purewack/numcalcium/docs/res/1.2.png

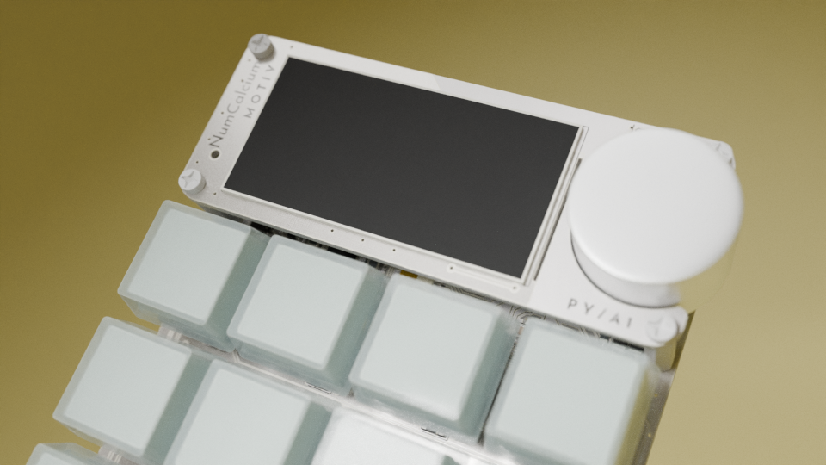
docs/res/1.2.png
