purewack/numcalcium/devlog/pya0-back.png

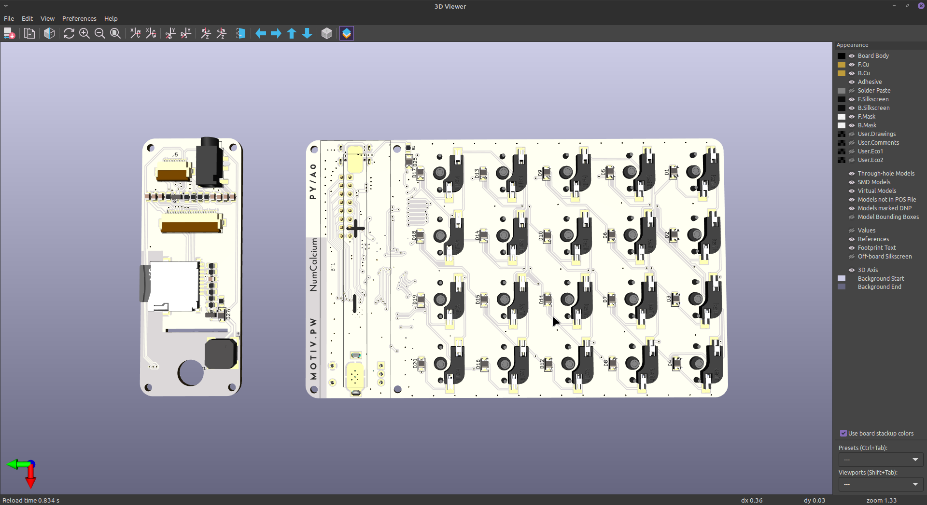
devlog/pya0-back.png
