purewack/numcalcium/devlog/pya0-front-back.png

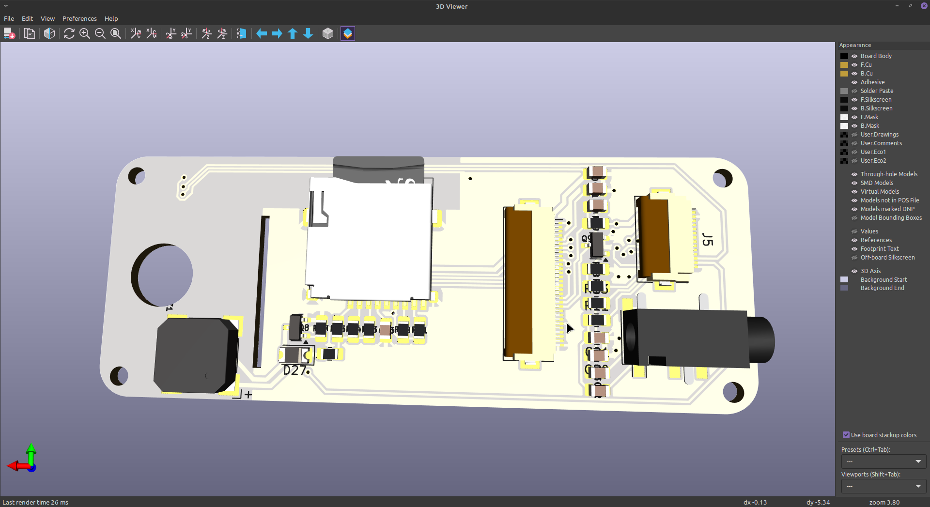
devlog/pya0-front-back.png
