purewack/numcalcium/devlog/pya0-front.png

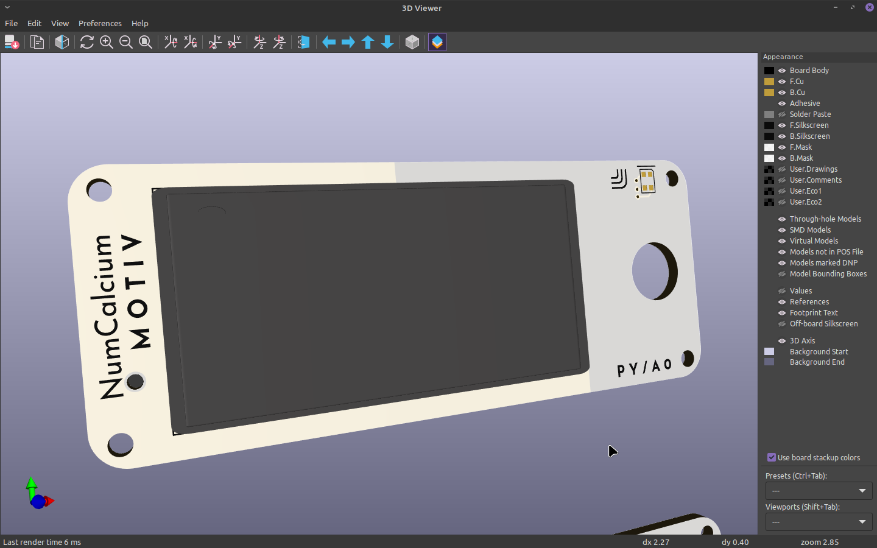
devlog/pya0-front.png
