purewack/numcalcium/devlog/pya0-main-all.png

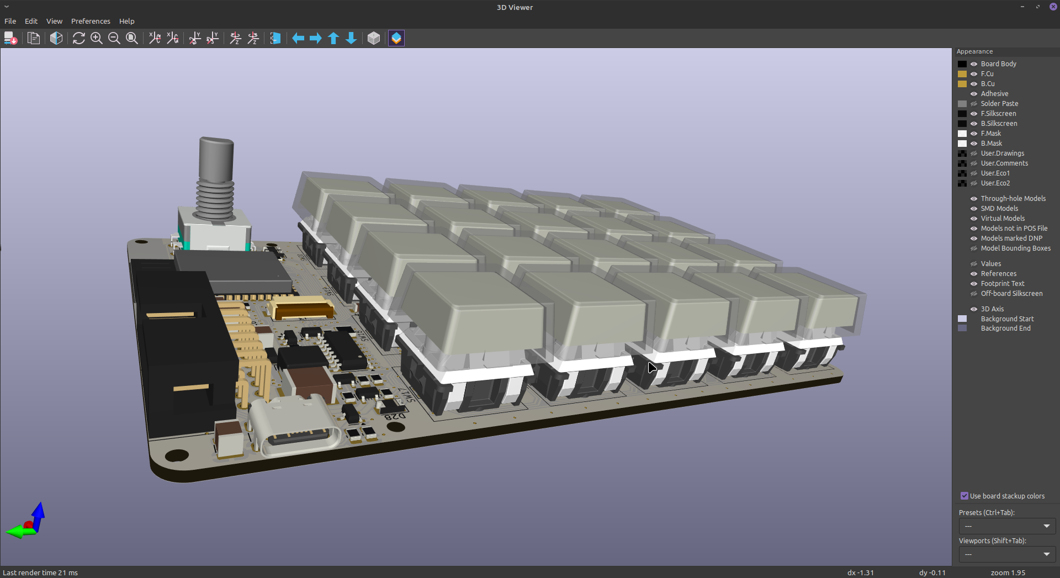
devlog/pya0-main-all.png
