purewack/numcalcium/devlog/pya1-back.png

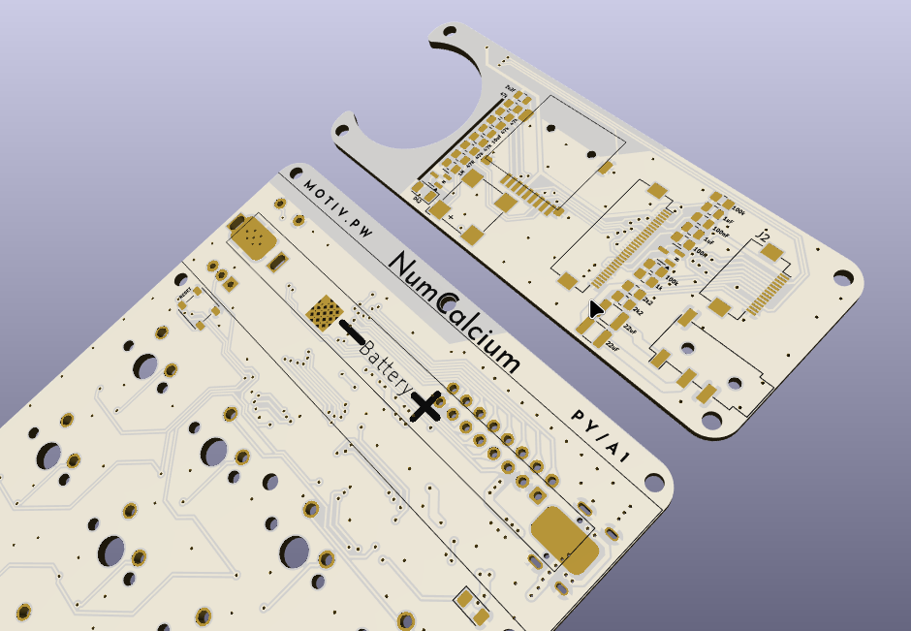
devlog/pya1-back.png
