purewack/numcalcium/devlog/pya1-bcu.png

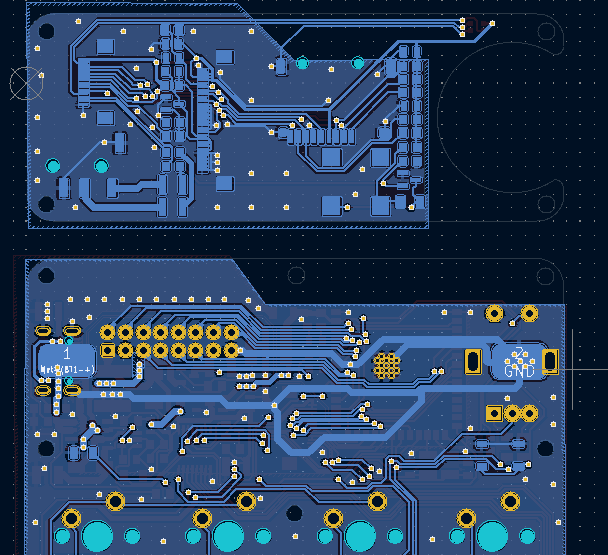
devlog/pya1-bcu.png
