purewack/numcalcium/devlog/pya1-cu.png

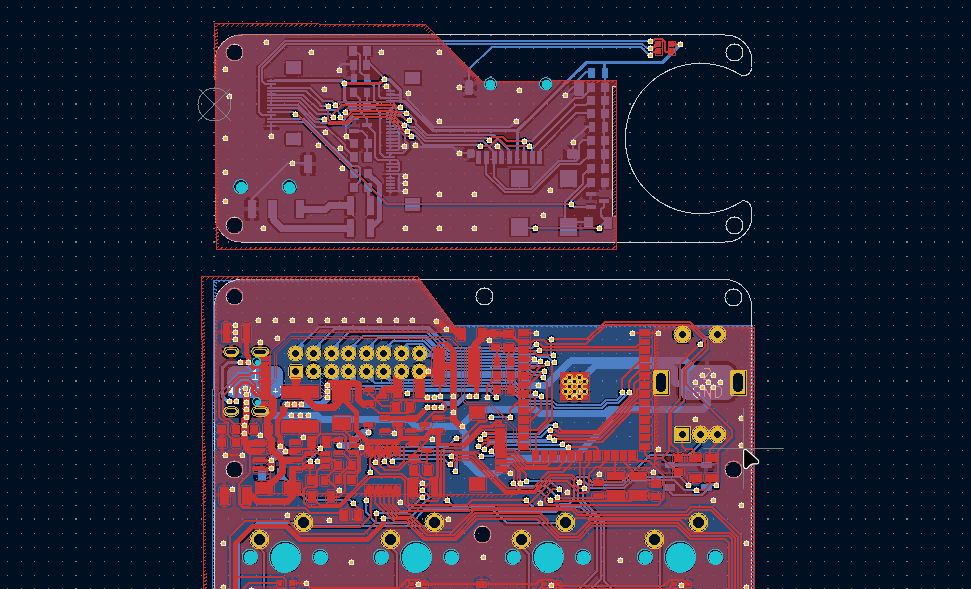
devlog/pya1-cu.png
