purewack/numcalcium/devlog/s3-front.png

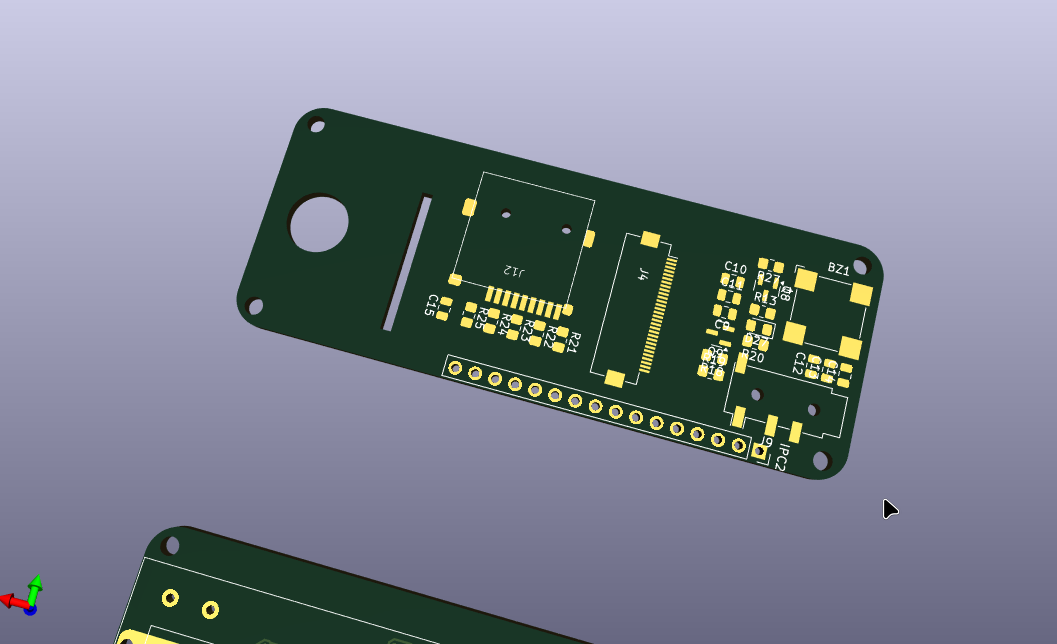
devlog/s3-front.png
