purewack/numcalcium/devlog/s3-gnd-alt-bcu.png

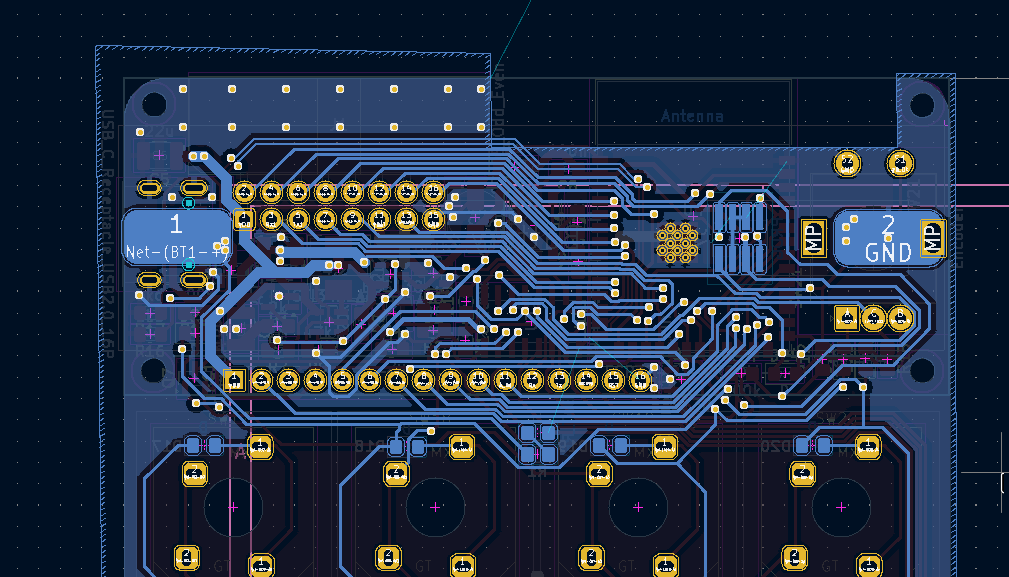
devlog/s3-gnd-alt-bcu.png
