purewack/numcalcium/numcalc/include/defs.h

#pragma once

#define SYS_PDOWN PB5

#define LCD_LIGHT PA6
#define LCD_CS PA4
#define LCD_DC PA3
#define LCD_CK PA5
#define LCD_RST PA2
#define LCD_MOSI PA7

#define SEG_A PB11
#define SEG_B PB10
#define SEG_C PB1
#define SEG_D PB0

#define ROW_A PA14
#define ROW_B PA15
#define ROW_C PB3
#define ROW_D PB4
#define ROW_E PB8
#define ROW_F PB9

#define B_OK PA8

#define GP_A PA0
#define GP_B PA1
#define COMMS_SDA PB7
#define COMMS_SDL PB6
#define COMMS_MOSI PB15
#define COMMS_MISO PB14
#define COMMS_CK   PB13
#define COMMS_CS PB12
#define COMMS_RX PA10
#define COMMS_TX PA9
