purewack/numcalcium/software-pya1/cmodules/board_sdcard.c

/*
 * This file is part of the MicroPython project, http://micropython.org/
 *
 * The MIT License (MIT)
 *
 * Copyright (c) 2019 Nicko van Someren
 *
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
 * THE SOFTWARE IS PROVIDED "AS IS", WITHOUT WARRANTY OF ANY KIND, EXPRESS OR
 * IMPLIED, INCLUDING BUT NOT LIMITED TO THE WARRANTIES OF MERCHANTABILITY,
 * FITNESS FOR A PARTICULAR PURPOSE AND NONINFRINGEMENT. IN NO EVENT SHALL THE
 * AUTHORS OR COPYRIGHT HOLDERS BE LIABLE FOR ANY CLAIM, DAMAGES OR OTHER
 * LIABILITY, WHETHER IN AN ACTION OF CONTRACT, TORT OR OTHERWISE, ARISING FROM,
 * OUT OF OR IN CONNECTION WITH THE SOFTWARE OR THE USE OR OTHER DEALINGS IN
 * THE SOFTWARE.
 */

#include <string.h>

#include "py/runtime.h"
#include "py/mphal.h"
#include "py/mperrno.h"
#include "extmod/vfs_fat.h"

#include "driver/sdspi_host.h"
#include "driver/sdmmc_host.h"
#include "sdmmc_cmd.h"
#include "esp_log.h"

#include "board.h"

// #define DEBUG 0
// #if DEBUG
// #define DEBUG_printf(...) ESP_LOGI("modsdcard", __VA_ARGS__)
// #else
// #define DEBUG_printf(...) (void)0
// #endif

//
// There are three layers of abstraction: host, slot and card.
// Creating an SD Card object will initialise the host and slot.
// Cards gets initialised by ioctl op==1 and de-inited by ioctl 2
// Hosts are de-inited in __del__. Slots do not need de-initing.
//

typedef struct _sdcard_obj_t {
    mp_obj_base_t base;
    mp_int_t flags;
    sdmmc_host_t host;
    // The card structure duplicates the host. It's not clear if we
    // can avoid this given the way that it is copied.
    sdmmc_card_t card;
} sdcard_card_obj_t;

const mp_obj_type_t board_sdcard_type;
// singleton object
static sdcard_card_obj_t sd_instance = {{&board_sdcard_type},0};

#define SDCARD_CARD_FLAGS_HOST_INIT_DONE 0x01
#define SDCARD_CARD_FLAGS_CARD_INIT_DONE 0x02

#define _SECTOR_SIZE(self) (self->card.csd.sector_size)


static esp_err_t sdcard_ensure_card_init(sdcard_card_obj_t *self, bool force) {
    if (force || !(self->flags & SDCARD_CARD_FLAGS_CARD_INIT_DONE)) {
        //DEBUG_printf("  Calling card init\n");

        esp_err_t err = sdmmc_card_init(&(self->host), &(self->card));
        if (err == ESP_OK) {
            self->flags |= SDCARD_CARD_FLAGS_CARD_INIT_DONE;
        } else {
            self->flags &= ~SDCARD_CARD_FLAGS_CARD_INIT_DONE;
        }
        //DEBUG_printf("  Card init returned: %d\n", self->flags);
        
        return err;
    } else {
        return ESP_OK;
    }
}

/******************************************************************************/
// MicroPython bindings
//
// Expose the SD card or MMC as an object with the block protocol.

// Create a new SDCard object
// The driver supports either the host SD/MMC controller (default) or SPI mode
// In both cases there are two "slots". Slot 0 on the SD/MMC controller is
// typically tied up with the flash interface in most ESP32 modules but in
// theory supports 1, 4 or 8-bit transfers. Slot 1 supports only 1 and 4-bit
// transfers. Only 1-bit is supported on the SPI interfaces.
// card = SDCard(slot=1, width=None, present_pin=None, wp_pin=None)

static mp_obj_t board_sdcard_make_new(const mp_obj_type_t *type, size_t n_args, size_t n_kw, const mp_obj_t *args) {
    // check arguments
    enum {
        ARG_freq,
    };
    static const mp_arg_t allowed_args[] = {
        // freq is valid for both SPI and SDMMC interfaces
        { MP_QSTR_freq,     MP_ARG_KW_ONLY | MP_ARG_INT, {.u_int = 40000000} },
    };
    mp_arg_val_t arg_vals[MP_ARRAY_SIZE(allowed_args)];
    mp_map_t kw_args;

    //DEBUG_printf("Making new SDCard\n");
    //DEBUG_printf("  Unpacking arguments\n");

    mp_map_init_fixed_table(&kw_args, n_kw, args + n_args);

    mp_arg_parse_all(n_args, args, &kw_args,
        MP_ARRAY_SIZE(allowed_args), allowed_args, arg_vals);

    if((sd_instance.flags & SDCARD_CARD_FLAGS_HOST_INIT_DONE)) return (mp_obj_t)&sd_instance;

    //DEBUG_printf("  Setting up host configuration\n");

    sd_instance.flags = 0;
    // Note that these defaults are macros that expand to structure
    // constants so we can't directly assign them to fields.
    int freq = arg_vals[ARG_freq].u_int;
    sdmmc_host_t _temp_host = SDSPI_HOST_DEFAULT();
    _temp_host.max_freq_khz = freq / 1000;
    _temp_host.slot = BOARD_SPI_SLOT_INTERNAL;
    sd_instance.host = _temp_host;

    //DEBUG_printf("  Calling host.init()\n");

    check_esp_err(sd_instance.host.init());
    sd_instance.flags |= SDCARD_CARD_FLAGS_HOST_INIT_DONE;

    //DEBUG_printf("  Returning new card object: %p\n", &sd_instance);
    return (mp_obj_t)&sd_instance;
}

static mp_obj_t sd_deinit(mp_obj_t self_in) {
    sdcard_card_obj_t *self = self_in;

    //DEBUG_printf("De-init host\n");

    if (self->flags & SDCARD_CARD_FLAGS_HOST_INIT_DONE) {
        if (self->host.flags & SDMMC_HOST_FLAG_DEINIT_ARG) {
            self->host.deinit_p(self->host.slot);
        } else {
            self->host.deinit();
        }
        // if (self->host.flags & SDMMC_HOST_FLAG_SPI) {
        //     // SD card used a (dedicated) SPI bus, so free that SPI bus.
        //     spi_bus_free(self->host.slot);
        // }
        self->flags &= ~SDCARD_CARD_FLAGS_HOST_INIT_DONE;
    }
    
    return mp_const_none;
}
static MP_DEFINE_CONST_FUN_OBJ_1(sd_deinit_obj, sd_deinit);

static mp_obj_t sd_info(mp_obj_t self_in) {
    sdcard_card_obj_t *self = self_in;
    // We could potential return a great deal more SD card data but it
    // is not clear that it is worth the extra code space to do
    // so. For the most part people only care about the card size and
    // block size.

    check_esp_err(sdcard_ensure_card_init((sdcard_card_obj_t *)self, false));

    uint32_t log_block_nbr = self->card.csd.capacity;
    uint32_t log_block_size = _SECTOR_SIZE(self);

    mp_obj_t tuple[2] = {
        mp_obj_new_int_from_ull((uint64_t)log_block_nbr * (uint64_t)log_block_size),
        mp_obj_new_int_from_uint(log_block_size),
    };
    return mp_obj_new_tuple(2, tuple);
}
static MP_DEFINE_CONST_FUN_OBJ_1(sd_info_obj, sd_info);

static mp_obj_t board_sdcard_readblocks(mp_obj_t self_in, mp_obj_t block_num, mp_obj_t buf) {
    sdcard_card_obj_t *self = self_in;
    mp_buffer_info_t bufinfo;
    esp_err_t err;

    err = sdcard_ensure_card_init((sdcard_card_obj_t *)self, false);
    if (err != ESP_OK) {
        return false;
    }

    mp_get_buffer_raise(buf, &bufinfo, MP_BUFFER_WRITE);
    err = sdmmc_read_sectors(&(self->card), bufinfo.buf, mp_obj_get_int(block_num), bufinfo.len / _SECTOR_SIZE(self));

    return mp_obj_new_bool(err == ESP_OK);
}
static MP_DEFINE_CONST_FUN_OBJ_3(board_sdcard_readblocks_obj, board_sdcard_readblocks);

static mp_obj_t board_sdcard_writeblocks(mp_obj_t self_in, mp_obj_t block_num, mp_obj_t buf) {
    sdcard_card_obj_t *self = self_in;
    mp_buffer_info_t bufinfo;
    esp_err_t err;

    err = sdcard_ensure_card_init((sdcard_card_obj_t *)self, false);
    if (err != ESP_OK) {
        return false;
    }

    mp_get_buffer_raise(buf, &bufinfo, MP_BUFFER_READ);
    err = sdmmc_write_sectors(&(self->card), bufinfo.buf, mp_obj_get_int(block_num), bufinfo.len / _SECTOR_SIZE(self));

    return mp_obj_new_bool(err == ESP_OK);
}
static MP_DEFINE_CONST_FUN_OBJ_3(board_sdcard_writeblocks_obj, board_sdcard_writeblocks);

static mp_obj_t board_sdcard_ioctl(mp_obj_t self_in, mp_obj_t cmd_in, mp_obj_t arg_in) {
    sdcard_card_obj_t *self = self_in;
    esp_err_t err = ESP_OK;
    mp_int_t cmd = mp_obj_get_int(cmd_in);

    switch (cmd) {
        case MP_BLOCKDEV_IOCTL_INIT:
            err = sdcard_ensure_card_init(self, true);
            return MP_OBJ_NEW_SMALL_INT((err == ESP_OK) ? 0 : -1);

        case MP_BLOCKDEV_IOCTL_DEINIT:
            // Ensure that future attempts to look at info re-read the card
            sd_deinit(self_in);
            return MP_OBJ_NEW_SMALL_INT(0); // success

        case MP_BLOCKDEV_IOCTL_SYNC:
            // nothing to do
            return MP_OBJ_NEW_SMALL_INT(0); // success

        case MP_BLOCKDEV_IOCTL_BLOCK_COUNT:
            err = sdcard_ensure_card_init(self, false);
            if (err != ESP_OK) {
                return MP_OBJ_NEW_SMALL_INT(-1);
            }
            return MP_OBJ_NEW_SMALL_INT(self->card.csd.capacity);

        case MP_BLOCKDEV_IOCTL_BLOCK_SIZE:
            err = sdcard_ensure_card_init(self, false);
            if (err != ESP_OK) {
                return MP_OBJ_NEW_SMALL_INT(-1);
            }
            return MP_OBJ_NEW_SMALL_INT(_SECTOR_SIZE(self));

        default: // unknown command
            return MP_OBJ_NEW_SMALL_INT(-1); // error
    }
}
static MP_DEFINE_CONST_FUN_OBJ_3(board_sdcard_ioctl_obj, board_sdcard_ioctl);

static const mp_rom_map_elem_t board_sdcard_locals_dict_table[] = {
    { MP_ROM_QSTR(MP_QSTR_info), MP_ROM_PTR(&sd_info_obj) },
    { MP_ROM_QSTR(MP_QSTR___del__), MP_ROM_PTR(&sd_deinit_obj) },
    { MP_ROM_QSTR(MP_QSTR_deinit), MP_ROM_PTR(&sd_deinit_obj) },
    // block device protocol
    { MP_ROM_QSTR(MP_QSTR_readblocks), MP_ROM_PTR(&board_sdcard_readblocks_obj) },
    { MP_ROM_QSTR(MP_QSTR_writeblocks), MP_ROM_PTR(&board_sdcard_writeblocks_obj) },
    { MP_ROM_QSTR(MP_QSTR_ioctl), MP_ROM_PTR(&board_sdcard_ioctl_obj) },
};

static MP_DEFINE_CONST_DICT(board_sdcard_locals_dict, board_sdcard_locals_dict_table);

MP_DEFINE_CONST_OBJ_TYPE(
    board_sdcard_type,
    MP_QSTR_SD,
    MP_TYPE_FLAG_NONE,
    make_new, board_sdcard_make_new,
    locals_dict, &board_sdcard_locals_dict
    );
