purewack/numcalcium/software-pya1/modules/numcalc.py

import _board
import __keys 
import __sleep
import __cartridge
import machine
import neopixel
import time
import __numcalcium_version

NUMCALC_VER = __numcalcium_version._version
NUMCALC_BUILD = __numcalcium_version._build

_board.init()
__sleep.exitLowPowerSleep()

def shutdown():
    clearLeds()
    __sleep.enterLowPowerSleep()

def runFromCartridge():
    __cartridge.run()

def burnToCartridge(data):
    __cartridge.burn(data)
    if(not __cartridge.check() == True):
        raise Exception('Error during burning, check wiring and chip')

class Keys(__keys.Keys):
    pass

class SD(_board.SD):
    pass

class DAC(_board.DAC):
    pass

class LCD(_board.Terminal):
    RED    = 0xf800
    GREEN  = 0x07e0
    BLUE   = 0x001f
    PURPLE = 0xf81f
    YELLOW = 0xffe0
    CYAN   = 0x07ff
    BLACK  = 0x0000
    WHITE  = 0xffff
    GRAY   = 0x8410
    
    WIDTH  = 320
    HEIGHT = 170
    
    def __init__(self):
        super().__init__()
        self._bl = None
        self.XN = self._CHARS_X
        self.YN = self._CHARS_Y
        self.FW = self.FONT_W
        self.FH = self.FONT_H
        self._XN_S1 = self._CHARS_X
        self._YN_S1 = self._CHARS_Y
        self._FW_S1 = self.FONT_W
        self._FH_S1 = self.FONT_H
        self.reset()
        self.setBacklight(127)

    def __del__(self):
        self.setBacklight(0)
        
    def reset(self):
        self.canvas = None
        self.font = None
        self.options(font=None,canvas=None,canvasWrapRegion=None,autoWrap=True,background=self.BLACK,foreground=self.WHITE,scale=1)
        self.clear()

    def clear(self):
        super().clear()
        self.cursor(0,0)

    def fill(self, x,y,w,h,color):
        if isinstance(color, str):
            super().fill(x,y,w,h,self.htmlTo565(color))
        elif isinstance(color, tuple):
            super().fill(x,y,w,h,self.rgbTo565(*color))
        else:
            super().fill(x,y,w,h,color)

    def plot(self, x,y,color):
        if isinstance(color, str):
            super().plot(x,y,self.htmlTo565(color))
        elif isinstance(color, tuple):
            super().plot(x,y,self.rgbTo565(*color))
        else:
            super().plot(x,y,color)

    def line(self, x,y,x2,y2,color):
        dy = (y2-y)
        dx = (x2-x)
        nx = dx*-1 if dx < 0 else dx
        ny = dy*-1 if dy < 0 else dy

        if(nx > ny):
            if(dx < 0):
                for i in range(dx,0,-1):
                    yy = ((i)*dy)//dx
                    self.plot((i+x),yy+y,color)
            else:
                for i in range(dx):
                    yy = ((i)*dy)//dx
                    self.plot((i+x),yy+y,color)
            
        else:
            if(dy < 0):
                for i in range(dy,0,-1):
                    xx = ((i)*dx)//dy
                    self.plot(xx+x,(i+y),color)
            else:
                for i in range(dy):
                    xx = ((i)*dx)//dy
                    self.plot(xx+x,(i+y),color)
    
    def createCanvas(self):
        self.canvas = bytearray(self.WIDTH*self.HEIGHT*2)
        self.options(canvas=self.canvas)
        return self.canvas
    
    def update(self,*args):
        if(self.canvas):
            if(len(args) == 4):
                x,y,w,h = args
                if(x >= self.WIDTH): return
                if(y >= self.HEIGHT): return
                if(x+w > self.WIDTH):
                    w -= x
                if(y+h > self.HEIGHT):
                    h -= y
                super().buffer(self.canvas,x,y,w,h,True)
            else:
                super().buffer(self.canvas,0,0,self.WIDTH,self.HEIGHT)
    
    def buffer(self,buf,x,y,width,height):
        super().buffer(buf,x,y,width,height)
    
    def loadBMP(self,file,headerOnly=False):
        return super().parseBMP(file,header_only=headerOnly)
    
    def bitmap(self, x, y, image, scale=1):
        if not self.canvas and scale > 1:
            raise ValueError('can only plot scaled bitmap on canvas')
        if isinstance(scale,int):
            return super().bitmap_scaled_integer(x, y, image, scale=scale)
        else:
            return super().bitmap_scaled_float(x, y, image, scale=scale)
   
    def print(self, *args):
        super().print(*args)

    def cursor(self, *args, **kwargs):
        
        s = super().options()['scale'] 
        ww = self.WIDTH
        hh = self.HEIGHT
        fh = self._FH_S1
        fw = self._FW_S1
        
        if('bottom' in kwargs and not isinstance(kwargs['bottom'],bool)):
            hh = kwargs['bottom']
        
        sfY = hh / (fh*s)
        
        ## GET
        if(not len(args)):
            c = super().cursor()
            x = c[0]
            y = c[1]
            if(kwargs.get('pixels',False)):
                # get from raw to px
                xx = (x*fw*s)
                yy = (y*fh*s)
                if(kwargs.get('bottom',False)):
                    yy = hh - yy + 0.0000001
                return (int(xx),int(yy))
    
            if(kwargs.get('bottom',False)):
                y = sfY - y
            return (float(x),float(y))
        if(not len(args) == 2):
            raise ValueError("Need both x and y positions")
        
        
        ## SET
        x = args[0]
        y = args[1]
        
        if(kwargs.get('pixels',False)):
            # set from px to raw
            x = x / fw / s
            y = y / fh / s
            if(kwargs.get('bottom',False)):
                y = sfY - y
            return super().cursor(x,y)
        
        if(kwargs.get('bottom',False)):
            y = sfY - y
        return super().cursor(x,y)
        
    def scale(self, scale=None):
        if scale == None:
            return super().options()['scale']
        
        self.XN = self._XN_S1 // scale
        self.YN = self._YN_S1 // scale
        self.FW = self._FW_S1 *  scale
        self.FH = self._FH_S1 *  scale
        super().options(scale=scale)
        
    def measure_text(self, text, pixels=False):
        s = self.scale()
        fh = self.FONT_H
        fw = self.FONT_W
        text = text.strip('\r').split('\n')
        cx = max(len(t) for t in text)
        cy = len(text)
        return (cx*fw*s,cy*fh*s) if pixels else (cx,cy)
    
    def background(self, color=None):
        if color == None:
            return super().options()['background']

        if isinstance(color, str):
            super().options(background=self.htmlTo565(color))
        elif isinstance(color, tuple):
            super().options(background=self.rgbTo565(*color))
        else:
            super().options(background=color)

    def foreground(self, color=None):
        if color == None:
            return super().options()['foreground']

        if isinstance(color, str):
            super().options(foreground=self.htmlTo565(color))
        elif isinstance(color, tuple):
            super().options(foreground=self.rgbTo565(*color))
        else:
            super().options(foreground=color)
    
    def color(self, color=None):
        return self.foreground(color)

    def bg(self, color=None):
        return self.background(color)

    def invert(self, state):
        super().options(invert=state)
    
    def options(self, **kwargs):

        if('foreground' in kwargs):
            if isinstance(kwargs['foreground'], str):
                kwargs['foreground'] = self.htmlTo565(kwargs['foreground'])
            elif isinstance(kwargs['foreground'], tuple):
                kwargs['foreground'] = self.rgbTo565(*kwargs['foreground'])

        if('background' in kwargs):
            if isinstance(kwargs['background'], str):
                kwargs['background'] = self.htmlTo565(kwargs['background'])
            elif isinstance(kwargs['background'], tuple):
                kwargs['background'] = self.rgbTo565(*kwargs['background'])
        
        if('scale' in kwargs):
            _s = kwargs['scale']
            kwargs.pop('scale')
            self.scale(_s)
        
        if('canvas' in kwargs):
            _cv = kwargs['canvas']
            kwargs.pop('canvas')
            if(not _cv):
                super().unsetCanvas()
            elif(_cv == True):
                super().setCanvas(self.canvas)
            else:
                super().setCanvas(_cv)
                self.canvas = _cv
            
        if('canvasWrapRegion' in kwargs):
            region = kwargs['canvasWrapRegion']
            kwargs.pop('canvasWrapRegion')
            if(region == None):
                super().canvasWrapRegion(self.WIDTH,self.HEIGHT)
            else:
                super().canvasWrapRegion(*region)
                
        if('font' in kwargs):
            cur = self.cursor(pixels=True)
            font = kwargs['font']
            kwargs.pop('font')
            if(font == None):
                super().unloadFont()
                self.XN = self._CHARS_X
                self.YN = self._CHARS_Y
                self.FW = self.FONT_W
                self.FH = self.FONT_H
                self._XN_S1 = self._CHARS_X
                self._YN_S1 = self._CHARS_Y
                self._FW_S1 = self.FONT_W
                self._FH_S1 = self.FONT_H
                self.font = None
            else:
                try:
                    data = font.data
                    self.font = font
                    self.FN = data.get('name','EXT')
                    self.FW = data['width']
                    self.FH = data['height']
                    self.XN = self.WIDTH//self.FW
                    self.YN = self.HEIGHT//self.FH
                    self._FW_S1 = data['width']
                    self._FH_S1 = data['height']
                    self._XN_S1 = self.WIDTH//self.FW
                    self._YN_S1 = self.HEIGHT//self.FH
                    super().loadFont(data['width'],data['height'],data['data'],data['count'])
                except:
                    raise ValueError('font module missing "data" attribute')
            self.cursor(*cur,pixels=True)
        return dict({'font': self.font, 'canvas': f"len:{len(self.canvas)}" if self.canvas else None, 'canvasWrapRegion': super().canvasWrapRegion()},**super().options(**kwargs))

    # brightness 0-127
    def setBacklight(self, brightness):
        if(not self._bl):
            self._bl = machine.PWM(machine.Pin.board.LCD_LED)
        self._bl.duty(brightness<<3)

    def framebufColor(self, color):
        return (color&0xff)<<8 | (color>>8)

    def rgbTo565(self, r, g, b):
        """Convert RGB values to RGB565."""
        r5 = (r >> 3) & 0x1F
        g6 = (g >> 2) & 0x3F
        b5 = (b >> 3) & 0x1F
        return (r5 << 11) | (g6 << 5) | b5

    def htmlTo565(self, html_color):
        """Convert HTML color string to RGB565."""
        html_color = html_color.lstrip('#')
        r = int(html_color[0:2], 16)
        g = int(html_color[2:4], 16)
        b = int(html_color[4:6], 16)
        return self.rgbTo565(r, g, b)


def tone(note=None, velocity=None):
    midi = note if note else 'c4'
    if(isinstance(note,str)):
        note_names = ['C', 'C#', 'D', 'D#', 'E', 'F', 'F#', 'G', 'G#', 'A', 'A#', 'B']
        octave = int(note[-1])
        note = note[:-1].upper()

        if note in note_names:
            midi = note_names.index(note) + 12 * (octave + 1)
        else:
            raise("Invalid note name")

    spk = machine.PWM(machine.Pin.board.BUZZER)
    if note == None:
        spk.freq(100)
        spk.duty(0)
        return
    spk.duty(velocity>>1)
    spk.freq(int(pow(2,(midi-69)/12)*440))


__neo = neopixel.NeoPixel(machine.Pin.board.LEDS,21)

def clearLeds():
    __neo.fill((0,0,0))
    __neo.write()

def statusLed(r,g,b):
    __neo[0] = (r,g,b)
    __neo.write()

def led(keyNumber,r,g,b):
    __neo[keyNumber + 1] = (r,g,b)
    __neo.write()



class Battery:
    def __init__(self):
        self.vbat = machine.ADC(machine.Pin.board.VBAT_MON)
        self.vbus = machine.Pin.board.CHR_STATE
        self.vbus.init(machine.Pin.IN,pull=machine.Pin.PULL_UP)
        self.DIFF_THRESH = 0.05

    def present(self):
        return True if self.voltage() else False

    def isAC(self):
        r = [0,0,0,0]
        for i in range(4):
            r[i] = not self.vbus.value()
            time.sleep(0.005)
        return bool((r[0]+r[1]+r[2]+r[3])/4)

    def voltage(self):
        r = [0,0,0,0]
        for i in range(4):
            r[i] = self.vbat.read_uv()*2/1000/1000
            time.sleep(0.005)

        self.isAC()
        avr = (r[0]+r[1]+r[2]+r[3])/4
        diff = max(*r) - min(*r);
        return 0 if diff > self.DIFF_THRESH else avr

    def level(self):
        v = self.voltage()
        low = 3
        high = 4.2
        return max(0,(v-low)/(high-low))
