purewack/numcalcium/software-pya1/cmodules/vt100.h

#ifndef LCD_VT100_H
#define LCD_VT100_H

#include "driver/spi_master.h"
#include "driver/gpio.h"
#include "freertos/FreeRTOS.h"
#include "freertos/task.h"
#include "font.h"


// #define COL_RED    0xf800
// #define COL_GREEN  0x07e0
// #define COL_BLUE   0x001f
// #define COL_PURPLE 0xf81f
// #define COL_YELLOW 0xffe0
// #define COL_CYAN   0x07ff
// #define COL_BLACK  0x0000
// #define COL_WHITE  0xffff

// Pin definitions
#define TFT_BL     46
#define TFT_CS     42
#define TFT_DC     45
#define TFT_MOSI   40
#define TFT_SCLK   39

//lcd config 
#define Y_OFFSET    35
#define X_SIZE      320
#define Y_SIZE      170
#define X_CHAR      (X_SIZE/FONT_WIDE)
#define Y_CHAR      (Y_SIZE/FONT_TALL)

#define FONT_COUNT_REDUCED 96

typedef struct {
    uint8_t xfCount;
    uint8_t xfWide;
    uint8_t xfTall;
    uint8_t *xfData; 
} font_t;

typedef struct {
    const uint8_t *buffer;
    bool partial;
    int size;
    int x;
    int y;
    int width;
    int height;
} buffer_data_t;

extern uint8_t lineBuf[1024*2];

// Utility functions for direct use
void driver_send_cmd(uint8_t cmd);
void driver_send_data(uint8_t data);

void driver_fill(int16_t x, int16_t y, int16_t w, int16_t h, uint16_t color, uint16_t* canvas);
void driver_pixel(int16_t x, int16_t y, uint16_t color, uint16_t* canvas);

void lcd_reset();
void driver_init();
void driver_setup();

void driver_print(const unsigned char* text, const uint32_t len, float *col, float *line, const uint16_t color, const uint16_t bg, const uint8_t scale, const bool autoWrap, font_t *font, uint16_t* canvas, const uint16_t cvW, const uint16_t cvH );

void driver_send_buffer(buffer_data_t buffer_data);
void driver_buffer_task(void *pvParameters);

#endif //LCD_VT100_H
