purewack/numcalcium/software-pya1/modules/__ulpio.py

data={'symbols': {'ulp_tick': 1342178136, 'bup': 1342178148, 'bok': 1342178144, 'bdown': 1342178152, 'turns': 1342178172, 'bhome': 1342178140, 'bscan': 1342178156}, 'binary': b'o\x00@\x00\x17\x11\x00\x00\x13\x01\xc1\xff\x11.\xa5"\x15&\x01\xa0\xb5g\x93\x87\x07\x80\x03\xa7G\x10\xb7\x06\x00\x80U\x8f#\xa2\xe7\x10\xb7\'\x00\x18\x93\x87\x17\x12\xaa\x97\tgq\x17\x8a\x07\xf9\x8f)g\xd9\x8f\x98C\xb7\x06\x08\x00U\x8f\x98\xc3\x98C\xb7\x06\xfa\xff\xfd\x16u\x8f\x98\xc3\x82\x80)g\x13\x07GA\x14C\x93\x07\x00@\xb3\x97\xa7\x00\x93\xf6\xf6?\xd5\x8f\x1c\xc3\x82\x80\xa9g\x93\x87GK\x94Cyw}\x17\xf9\x8e\x94\xc3\xa9g\x93\x87\x87K\x94C7\x06@\x00\xb7\x05\x80\x00u\x8f\x98\xc3\xa9g\x93\x87\x07A\x98C\xb7\x06 \x00\x01H\x13w\xf7?Q\x8f\x98\xc3\x98C\x05C\xa1H\x13w\xf7?M\x8f\x98\xc3\xa9g\x93\x87\x87@\x98C\x13w\xf7?Q\x8f\x98\xc3\x98C\x13w\xf7?M\x8f\x98\xc3\x98C\x13w\xf7?U\x8f\x98\xc3)g\x13\x07G@\xb3\x16\x03\x01\xe9\x8e\x93\xf6\xf6\x0f\x9d\xca\x14C\x93\xf6\xf6?\xcd\x8e\x14\xc3\x14C\x05\x08\x93\xf6\xf6?\xd1\x8e\x14\xc3\x94C\x93\xf6\xf6?\xd1\x8e\x94\xc3\xe3\x1a\x18\xfd\x1cC\xb7\x06 \x00\x93\xf7\xf7?\xd5\x8f\x1c\xc3\x82\x80\x94C\x93\xf6\xf6?\xcd\x8e\x94\xc3\xf1\xb7A\x111E\x06\xc6\r75E9?\xa9g\x93\x87GK\x98C\x89f\xb2@U\x8f\x98\xc3\xa9g\x93\x87\x87K\x98CU\x8f\xa9f\x98\xc3\x93\x86FB\x9cB\x98B\x88B\xd9\x83Y\x83\x91\x8b\t\x8bY\x81\xd9\x8f\x05\x89]\x8dA\x01\x82\x80\xa9g\x83\xa7GB\xa9\x83\x85\x8b\x93\xc7\x17\x00\x01\x11# \xf06\x03\'\xc051E\x06\xce\xd9\x8f#.\xf04"\xcc&\xcaJ\xc8N\xc6R\xc4V\xc2Z\xc0\xbd55E\xad5-E\x9d59E\x8d5\xa9g\x93\x87\xc7K\x98C\x89fU\x8f\x98\xc3\x98C\xb7\x06\x00\x10\x03$@7U\x8f\x98\xc3\xa9g\x93\x87GK\x98C\x01I\x81DU\x8f\x98\xc3\xa9g\x93\x87\x87K\x98C\x05K\x8dJU\x8f\x98\xc3)g\x13\x07\x07A\x1cC\xb7\x06 \x00\x1dJ\x93\xf7\xf7?\xd5\x8f\x1c\xc3#(\x8063\x15\x9b\x00\x8d59?\xb3\x87T\x03\x85\x043\x15\xf5\x003i\xa9\x00#* 7\xe3\x93D\xff\x03&@6\x93G\xf9\xff7\x07\x10\x00}\x17\xe1\x8f\xf9\x8f\xd1\x8f\x13D\xf4\xff#"\xf063t$\x01y\x8c\x03\'\x806\x13\x05\x00\x08Y\x8c#$\x806#& 7\x11=\x03$\x807\xf15\xadG\n\x04A\x8d=\x89#,\xa06c\x1e\xf5\x08\x83\'\xc07\x13\xa7\x17\x003\x07\xe0@\xf9\x8f\xfd\x17#.\xf06\xa9i\x03\xa7IK\xf9w\xfd\x17}\x8f#\xaa\xe9J\x03\xa7\x89K\x13\x84\xc9K\x93\x84\tK}\x8f#\xac\xe9J\x18@1E}\x8f\x18\xc0\x98@\xf9\x8f\x9c\xc0y;5Ei;9EY;-EI;\x03\xa7IK\xb7\x07\xf8\xff\xfd\x17}\x8f#\xaa\xe9J\x03\xa7\x89K\xf2@BI}\x8f#\xac\xe9J\x98@\xb2I"J}\x8f\x98\xc0\x18@\xd2D\x92J\xf9\x8f\x1c\xc0\x83\'\x805bD\x02K\x85\x07#,\xf04\x01E\x05a\x82\x80\xe3\x1e\x95\xf6\x83\'\xc07\x13\xc7\xf7\xff}\x87\xf9\x8f\x85\x07\x9d\xb7\xa1g\x93\x87G\x10\x98C\xb7\x06\xc0\xfd\xfd\x16u\x8f\x98\xc3\x82\x80\xa1g\x93\x87G\x10\x98C\xb7F\xc0\xff\xfd\x16u\x8f\xb7\xc6\x0f\x00U\x8f\x98\xc3\x98C\xb7\x06@\x02U\x8f\x98\xc3\x01\xa0'}
