purewack/numcalcium/tests/vbat_raw.py

import numcalc
import time
import os
import machine

vbat = machine.ADC(machine.Pin.board.VBAT_MON)
chrg = machine.Pin.board.CHR_STATE
chrg.init(machine.Pin.IN,pull=machine.Pin.PULL_UP)
lcd = numcalc.LCD()
k = numcalc.Keys()

def dischargeCycle():
    for i in range(20):
        time.sleep(0.01)
        numcalc.led(i,200,200,200)
    for i in range(20):
        time.sleep(0.01)
        numcalc.led(i,0,0,0)

discharing = False

while True:
    if(k.isAnyDown()):
        k.clearAll()
        discharing = not discharing

    if discharing:
        dischargeCycle()

    lcd.clear() 
    lcd.print("VBAT",vbat.read_uv()*2/1000/1000)
    lcd.print("Charging",not chrg.value())
    print(vbat.read_uv(), chrg.value())
    print("-----")
    time.sleep(0.1)
