purewack/numcalcium/software-pya1/dev-scripts/font_gohu13inv.py

# 104 character set: gohu13inv

data={'width': 8, 'height': 13, 'data': bytearray(b'\x00\x00\xfe\x0fV\r\xaa\nV\r\xaa\n\xfe\x0f\x00\x00\x00\x00\x00\x00\x00\x00\x00\x00\x00\x00\x00\x00\x00\x00\x00\x00\x00\x00\x00\x00\x00\x00\x00\x00\xec\x07\x00\x00\x00\x00\x00\x00\x00\x00\x00\x0e\x00\r\x00\x00\x00\r\x00\x0e\x00\x00\x00\x00 \x01 \x01\xfc\x0f \x01\xfc\x0f \x01 \x01\x00\x00\x88\x03D\x04D\x04\xff\x1fD\x04D\x048\x02\x00\x00\x00\x04\x0c\n0\n\xc8\x04\x14\x03\x14\x0c\x08\x00\x00\x00\x00\x00x\x00\x84\x06\x84\tD\t8\x06D\x00\x00\x00\x00\x00\x00\x00\x00\x00\x00\x00\x00\x0e\x00\x00\x00\x00\x00\x00\x00\x00\x00\x00\xe0\x01\x18\x06\x04\x08\x02\x10\x00\x00\x00\x00\x00\x00\x02\x10\x04\x08\x18\x06\xe0\x01\x00\x00\x00\x00\x00\x00 \x02@\x01\x80\x00\xf0\x07\x80\x00@\x01 \x02\x00\x00\x80\x00\x80\x00\x80\x00\xf0\x07\x80\x00\x80\x00\x80\x00\x00\x00\x00\x00\x00\x00\x00\x00\x00\x00\x1a\x00\x1c\x00\x00\x00\x00\x00\x00\x00@\x00@\x00@\x00@\x00@\x00@\x00\x00\x00\x00\x00\x18\x00\x18\x00\x00\x00\x00\x00\x00\x00\x00\x00\x00\x00\x00\x00\x06\x00\x18\x00`\x00\x80\x01\x00\x06\x00\x18\x00\x00\xf0\x07H\x08\x88\x08\x08\t\x08\n\xf0\x07\x00\x00\x00\x00\x00\x01\x00\x02\x00\x04\xf8\x0f\x00\x00\x00\x00\x00\x00\x00\x00\x18\x06(\x08H\x08\x88\x08\x08\t\x08\x06\x00\x00\x00\x00\x10\x04\x08\x08\x88\x08\x88\x08\x88\x08p\x07\x00\x00\x00\x00\xc0\x00@\x01@\x02@\x04\xf8\x0f@\x00\x00\x00\x00\x00\x10\x0f\x08\t\x08\t\x08\t\x08\t\xf0\x08\x00\x00\x00\x00\xf0\x07\x08\t\x08\t\x08\t\x08\t\xf0\x00\x00\x00\x00\x00\x00\x08\x00\x088\x08\xc0\x08\x00\x0b\x00\x0c\x00\x00\x00\x00p\x07\x88\x08\x88\x08\x88\x08\x88\x08p\x07\x00\x00\x00\x00\x00\x07\x88\x08\x88\x08\x88\x08\x90\x08\xe0\x07\x00\x00\x00\x00\x00\x00\x00\x00\x00\x000\x060\x06\x00\x00\x00\x00\x00\x00\x00\x00\x00\x00\x00\x004\x068\x06\x00\x00\x00\x00\x00\x00\x80\x00@\x01 \x02\x10\x04\x08\x08\x00\x00\x00\x00\x00\x00\x00\x00\x10\x01\x10\x01\x10\x01\x10\x01\x10\x01\x10\x01\x00\x00\x00\x00\x08\x08\x10\x04 \x02@\x01\x80\x00\x00\x00\x00\x00\x00\x08\x00\x10X\x10\x80\x10\x00\x11\x00\x0e\x00\x00\x00\x00\xf8\x07\x04\x08\xe4\t\x14\n\x14\n$\n\xf4\x07\x00\x00\x00\x00\xf8\x07\x80\x08\x80\x08\x80\x08\x80\x08\xf8\x07\x00\x00\x00\x00\xf8\x0f\x88\x08\x88\x08\x88\x08\x88\x08p\x07\x00\x00\x00\x00\xf0\x07\x08\x08\x08\x08\x08\x08\x08\x08\x10\x04\x00\x00\x00\x00\xf8\x0f\x08\x08\x08\x08\x08\x08\x10\x04\xe0\x03\x00\x00\x00\x00\xf8\x0f\x88\x08\x88\x08\x88\x08\x08\x08\x08\x08\x00\x00\x00\x00\xf8\x0f\x80\x08\x80\x08\x80\x08\x00\x08\x00\x08\x00\x00\x00\x00\xf0\x07\x08\x08\x08\x08\x88\x08\x88\x08\xf0\x04\x00\x00\x00\x00\xf8\x0f\x80\x00\x80\x00\x80\x00\x80\x00\xf8\x0f\x00\x00\x00\x00\x00\x00\x08\x08\xf8\x0f\x08\x08\x00\x00\x00\x00\x00\x00\x00\x000\x00\x08\x00\x08\x00\x08\x00\x08\x00\xf0\x0f\x00\x00\x00\x00\xf8\x0f\x80\x00@\x01 \x02\x10\x04\x08\x08\x00\x00\x00\x00\xf8\x0f\x08\x00\x08\x00\x08\x00\x08\x00\x08\x00\x00\x00\xf8\x0f\x00\x04\x00\x02\x80\x01\x00\x02\x00\x04\xf8\x0f\x00\x00\x00\x00\xf8\x0f\x00\x06\x80\x01`\x00\x18\x00\xf8\x0f\x00\x00\x00\x00\xf0\x07\x08\x08\x08\x08\x08\x08\x08\x08\xf0\x07\x00\x00\x00\x00\xf8\x0f\x80\x08\x80\x08\x80\x08\x80\x08\x00\x07\x00\x00\x00\x00\xf0\x07\x08\x08\x08\x08h\x08\x10\x08\xec\x07\x00\x00\x00\x00\xf8\x0f\x80\x08\x80\x08\xc0\x08\xa0\x08\x18\x07\x00\x00\x00\x00\x10\x07\x88\x08\x88\x08\x88\x08\x88\x08p\x04\x00\x00\x00\x08\x00\x08\x00\x08\xf8\x0f\x00\x08\x00\x08\x00\x08\x00\x00\x00\x00\xf0\x0f\x08\x00\x08\x00\x08\x00\x08\x00\xf0\x0f\x00\x00\x00\x00\x00\x0f\xe0\x00\x18\x00\x18\x00\xe0\x00\x00\x0f\x00\x00\xc0\x0f8\x00@\x00\x80\x03@\x008\x00\xc0\x0f\x00\x00\x00\x00\x18\x0c`\x03\x80\x00\x80\x00`\x03\x18\x0c\x00\x00\x00\x0c\x00\x03\x80\x00x\x00\x80\x00\x00\x03\x00\x0c\x00\x00\x00\x008\x08H\x08\x88\x08\x08\t\x08\n\x08\x0c\x00\x00\x00\x00\x00\x00\x00\x00\xfc\x1f\x04\x10\x04\x10\x00\x00\x00\x00\x00\x00\x00\x18\x00\x06\x80\x01`\x00\x18\x00\x06\x00\x00\x00\x00\x00\x00\x00\x04\x10\x04\x10\xfc\x1f\x00\x00\x00\x00\x00\x00\x00\x00\x00\x02\x00\x04\x00\x08\x00\x04\x00\x02\x00\x00\x00\x00\x02\x00\x02\x00\x02\x00\x02\x00\x02\x00\x02\x00\x02\x00\x02\x00\x00\x00\x00\x00\x00\x08\x00\x04\x00\x02\x00\x00\x00\x00\x00\x00p\x00\x88\x02\x88\x02\x88\x02\x90\x02\xf8\x01\x00\x00\x00\x00\xf8\x1f\x08\x01\x08\x02\x08\x02\x08\x02\xf0\x01\x00\x00\x00\x00\xf0\x01\x08\x02\x08\x02\x08\x02\x08\x02\x10\x01\x00\x00\x00\x00\xf0\x01\x08\x02\x08\x02\x08\x02\x10\x02\xf8\x1f\x00\x00\x00\x00\xf0\x01H\x02H\x02H\x02H\x02\xc8\x01\x00\x00\x00\x00\x00\x00\xf8\x0f\x00\x11\x00\x11\x00\x11\x00\x00\x00\x00\x00\x00\xf0\x01\t\x02\t\x02\t\x02\x11\x02\xfe\x03\x00\x00\x00\x00\xf8\x1f\x00\x01\x00\x02\x00\x02\x00\x02\xf8\x01\x00\x00\x00\x00\x00\x02\x00\x02\xf8\x1b\x08\x00\x08\x00\x00\x00\x00\x00\x00\x00\x01\x00\x01\x00\x01\x02\xfe\x1b\x00\x00\x00\x00\x00\x00\x00\x00\xf8\x1f@\x00@\x00\xa0\x00\x10\x01\x08\x00\x00\x00\x00\x00\x00\x00\x00\x10\xf0\x1f\x08\x00\x08\x00\x08\x00\x00\x00\x00\x00\xf8\x03\x00\x02\x00\x02\xf8\x03\x00\x02\x00\x02\xf8\x01\x00\x00\xf8\x03\x00\x02\x00\x02\x00\x02\x00\x02\xf8\x01\x00\x00\x00\x00\xf0\x01\x08\x02\x08\x02\x08\x02\x08\x02\xf0\x01\x00\x00\x00\x00\xff\x03\x08\x01\x08\x02\x08\x02\x08\x02\xf0\x01\x00\x00\x00\x00\xf0\x01\x08\x02\x08\x02\x08\x02\x10\x02\xff\x03\x00\x00\x00\x00\xf8\x03\x00\x01\x00\x02\x00\x02\x00\x02\x00\x01\x00\x00\x00\x00\x88\x01H\x02H\x02H\x02H\x020\x00\x00\x00\x00\x00\x00\x00\x00\x02\xf0\x1f\x08\x02\x08\x02\x00\x00\x00\x00\x00\x00\xf0\x03\x08\x00\x08\x00\x08\x00\x10\x00\xf8\x03\x00\x00\x00\x00\x80\x03`\x00\x18\x00\x18\x00`\x00\x80\x03\x00\x00\x00\x00\xe0\x03\x18\x00 \x00\xc0\x00 \x00\x18\x00\xe0\x03\x00\x00\x18\x03\xa0\x00@\x00@\x00\xa0\x00\x18\x03\x00\x00\x00\x00\xf0\x03\t\x00\t\x00\t\x00\x11\x00\xfe\x03\x00\x00\x00\x00\x18\x02(\x02H\x02\x88\x02\x08\x03\x08\x02\x00\x00\x00\x00@\x00@\x00@\x00\xbc\x0f\x02\x10\x02\x10\x02\x10\x00\x00\x00\x00\x00\x00\x00\x00\xfe\x1f\x00\x00\x00\x00\x00\x00\x00\x00\x02\x10\x02\x10\x02\x10\xbc\x0f@\x00@\x00@\x00\x00\x00`\x00\x80\x00\x80\x00@\x00 \x00 \x00\xc0\x00\x00\x00A\x10\x00\x00\x14\x07\xaa\x08\xaa\x08\x14\x07\x00\x00A\x10@\x10\x00\x00\x10\x00\xaa\x08\xaa\x0f\x9c\x00\x00\x00@\x10A\x10\x00\x00\x9e\t\xa4\n\xa4\n\x9e\x04\x00\x00A\x10A\x10\x00\x00\xbe\x08\xaa\n\xaa\n\x14\x05\x00\x00A\x10A\x10\x00\x00>\x0e"\x02"\x02\xa2\x0f\x00\x00A\x10A\x10\x00\x00\xbe\x0e\xa2\n\xa2\n\x1c\t\x00\x00A\x10A\x10\x00\x00>\x07\xaa\n\xaa\n*\x01\x00\x00A\x10A\x10\x00\x00\xbe\x08(\t(\n(\x0c\x00\x00A\x10')}
