purewack/numcalcium/tests/display_canvas.py

import numcalc
import framebuf
# import bmp

terminal = numcalc.LCD()
print(terminal.options())
terminal.createCanvas()

terminal.background(terminal.GRAY)
terminal.color(terminal.BLACK)
terminal.clear()
terminal.options(rgbSwap=False,scale=1,invert=False)


terminal.fill(48,48,16,16,terminal.GREEN)
for i in range(128):
    terminal.plot(i,i,terminal.GREEN)

for i in range(128):
    terminal.plot(64,i,terminal.BLUE)

for i in range(128):
    terminal.plot(128-i,i,terminal.RED)


terminal.cursor(0,0)
terminal.color(terminal.WHITE)
terminal.background(terminal.BLACK)
terminal.print("hello HELLO\n123 !#@\n\rYO deleted\b\b\ro")

terminal.color(terminal.YELLOW)
terminal.background(0x03c8)
terminal.print("colored text and background")

fbuf = framebuf.FrameBuffer(bytearray(64 * 32 * 2), 64, 32, framebuf.RGB565)
fbuf.rect(0,0,64,16,terminal.framebufColor(0x03c8),True)
fbuf.text('Buffer!', 0, 0, 0xffff)

fbuf.rect(0,16,64,16,terminal.framebufColor(terminal.YELLOW),True)
fbuf.text('Yellow', 0, 16, 0)

terminal.fill(0,0,320,2,terminal.RED)
terminal.fill(0,0,2,170,terminal.RED)
terminal.fill(0,169,320,2,terminal.RED)
terminal.fill(319,0,2,170,terminal.RED)

terminal.update()

terminal.buffer(fbuf,320//2,70,64,32)


terminal.background(0xffff)
terminal.foreground(0)
terminal.clear()
terminal.plot(0,0,0)
terminal.plot(10,10,0)
print(terminal.options())
print(terminal.options())
terminal.options(canvasWrapRegion=(100,80))
terminal.cursor(3,3,pixels=True)
print(terminal.options())
terminal.print('canvas wrap test')

terminal.update(64,64,100,80)

# terminal.update()

# with open("test.bmp","rb") as _f:
# #    img = bmp.parse(_f)
#     img = terminal.parseBMP(_f)
#     terminal.bitmap(320//2,64,img)
